mydhily-mr/aiot-inventory-predictor/docs/d8_ultrasonic.md

# Individual Sensor Testing

# Ultrasonic with MAX32630fthr

### Goal

Interfacing SSD1306 Oled display with MAX32630fthr board.

### Final working setup

**Hardware:** MAX32630FTHR, NHX711 Weight sensor 5Kg

**Wiring** :
| Weight Sensor  | MAX32630FTHR |
|---|---|
| GND | GND |
| VCC | 3V3 |
| TRIG | P5_6  |
| ECHO | P4_0  |

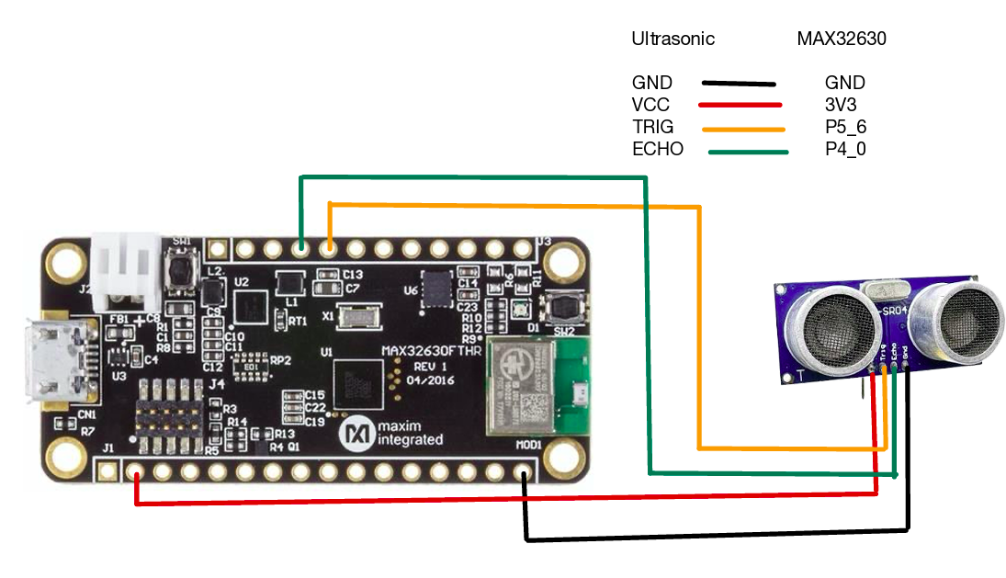
[picture p96: images/ultra_sc.png]
  — Ultrasonic Connection.

**Code Snippet:**
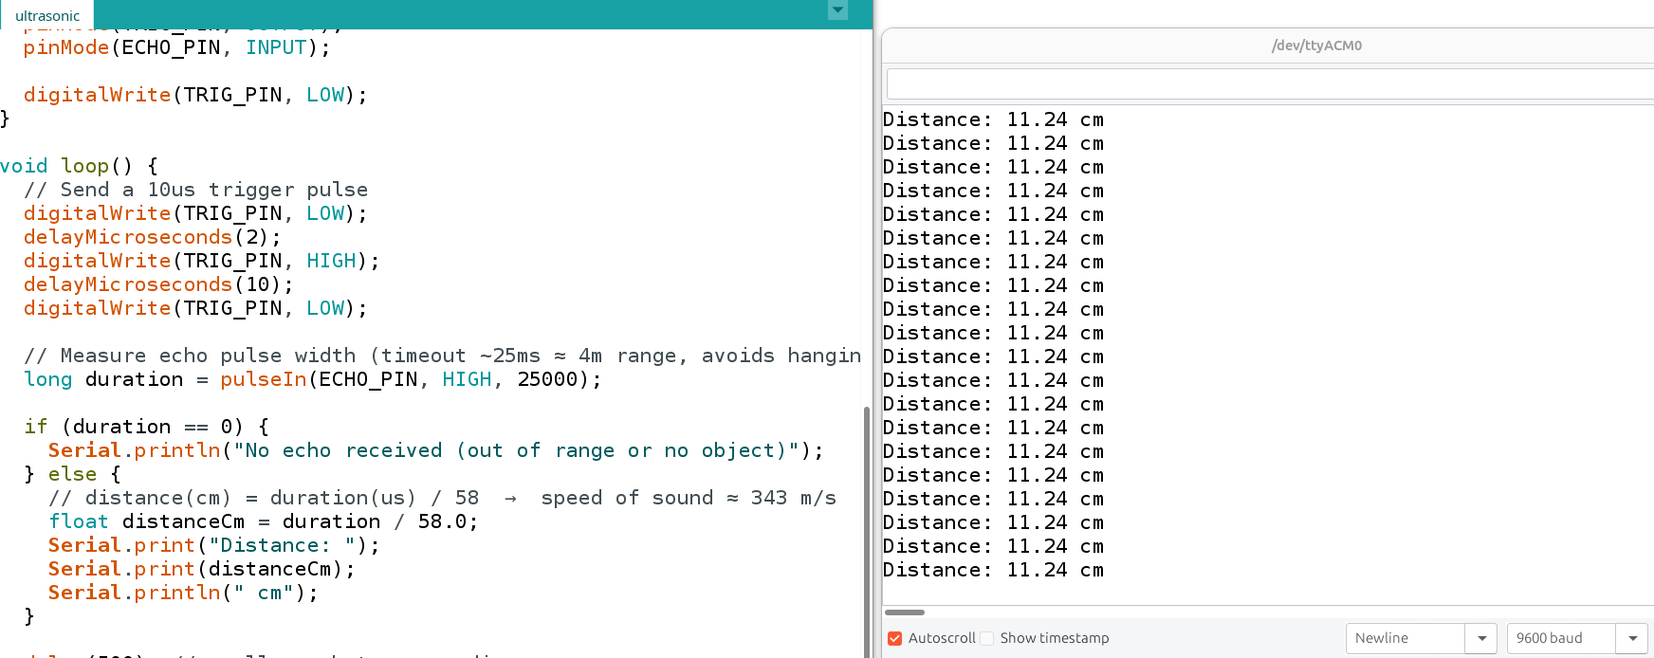
[picture p97: images/ul.png]
 — Ultrasonic
## Output:
wifi serial monitor — Ultrasonic
