mydhily-mr/aiot-inventory-predictor/docs/d10_buzzer.md

# Individual Sensor Testing

# Piezo Buzzer with MAX32630 FTHR

### Goal

Interfacing Buzzer with MAX32630fthr board.

**Schematic:**
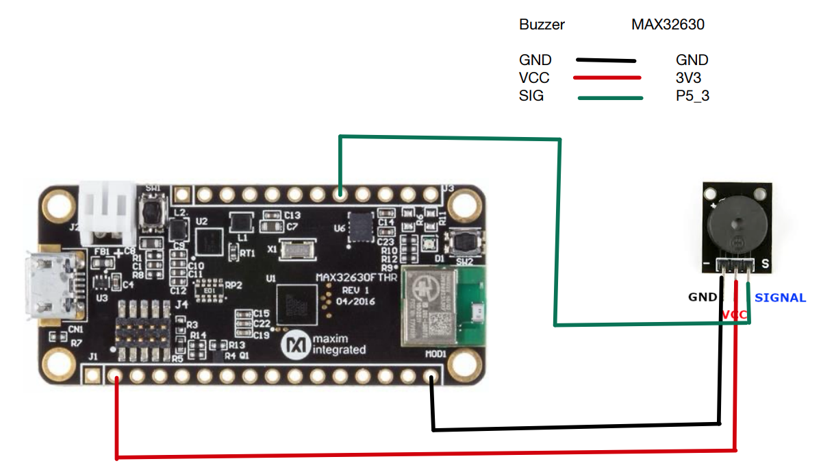
[picture p98: images/bzr.png]
 — Buzzer

**Wiring** :
| RYG  | MAX32630FTHR |
|---|---|
| GND | GND |
| VCC | 3V3 |
| SIG | P5_3  |

**Code Snippet:**
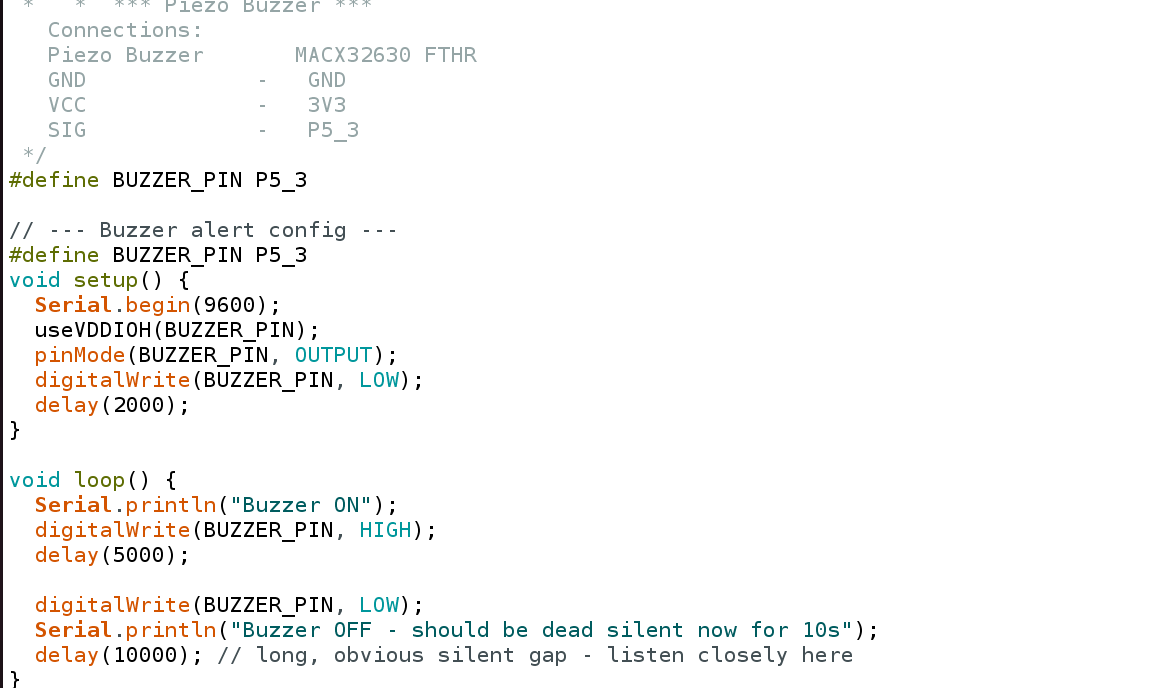
[picture p99: images/bzr_cd.png]
 —Buzzer
