mydhily-mr/aiot-inventory-predictor/docs/d12_pir.md

# Individual Sensor Testing

# PIR with MAX32630 FTHR

### Goal

Interfacing PIR  with MAX32630fthr board.

**Schematic:**
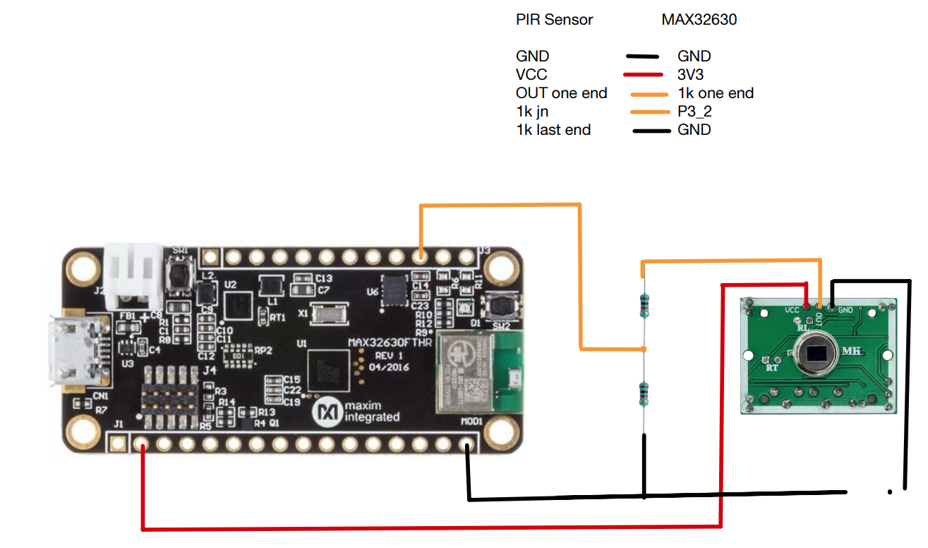
[picture p100: images/pir.png]
ryg led
 — PIR
