mydhily-mr/aiot-inventory-predictor/docs/d6_weight_sensor.md

# Individual Sensor Testing

# HX711 Weight Sensor with MAX32630FTHR board

### Goal

Interfacing HX711 weight sensor with MAX32630fthr board.

### Final working setup

**Hardware:** MAX32630FTHR, NHX711 Weight sensor 5Kg

**Wiring** :
| Weight Sensor  | MAX32630FTHR |
|---|---|
| GND | GND |
| VCC | 3V3 |
| DT | P5_5 (pin 45 in software) |
| DSCK  | P5_4 (pin 45 in software) |

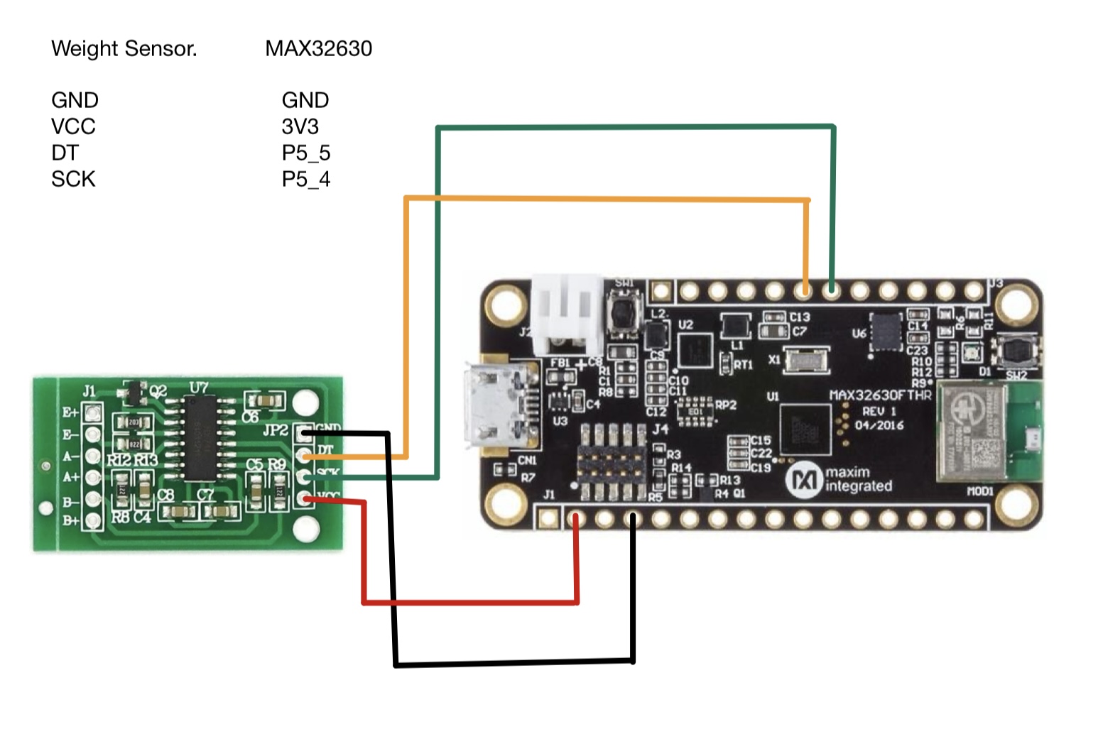
[picture p101: images/weight_sensor.PNG]
  — weight_sensor Connection.

**Code Snippet:**
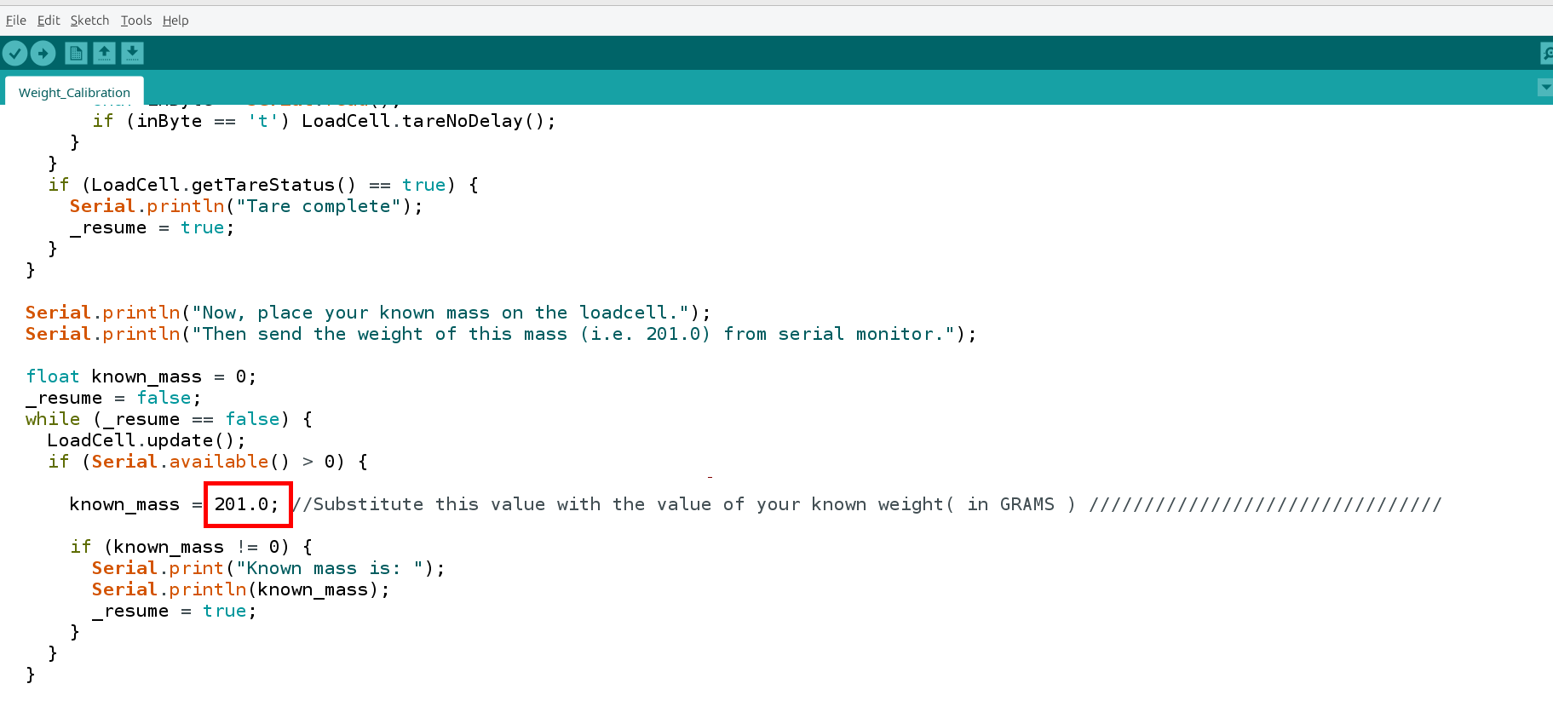
[picture p102: images/weight_sens.png]
 — weight_sensor Known mass value to change.

## Output:

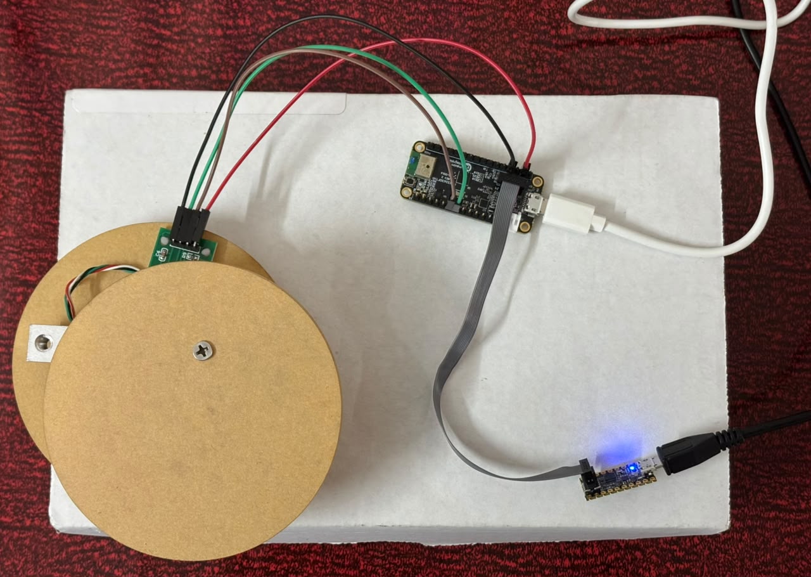
[picture p103: images/weight_output1.jpeg]
  — weight_sensor connection.

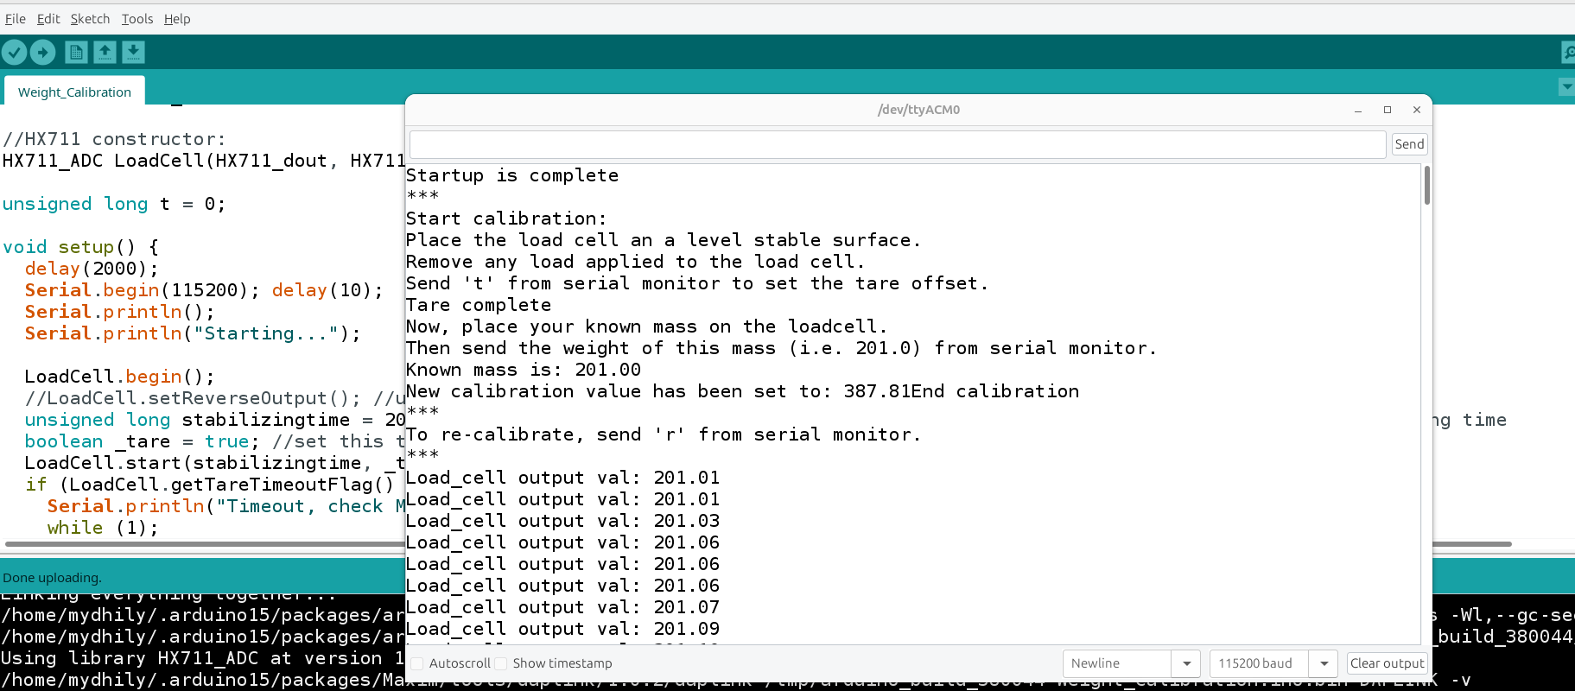
[picture p104: images/weight_sensor_output.png]
  — weight_sensor calibration output with known weight.

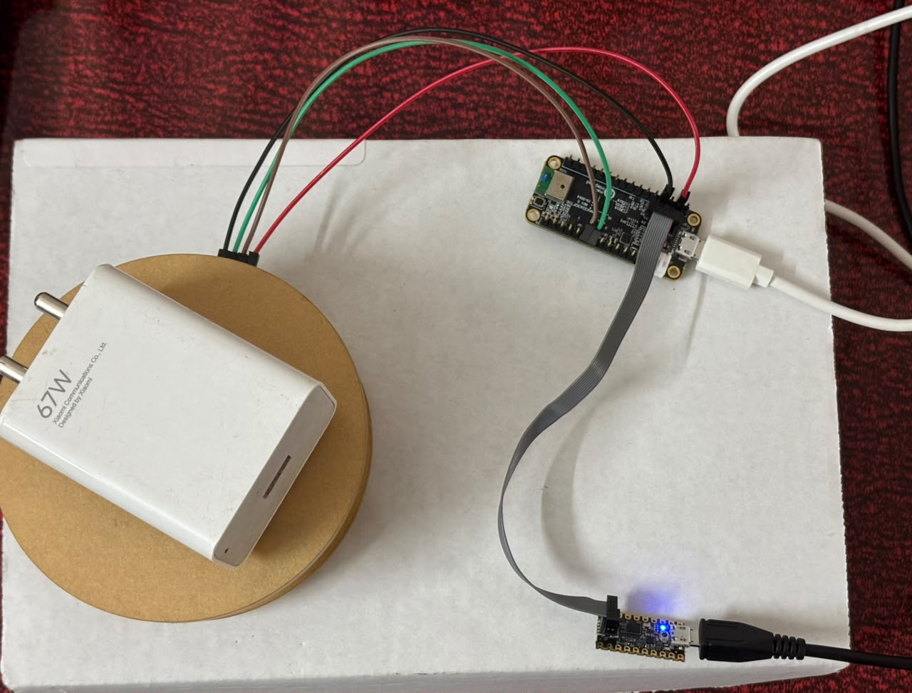
[picture p105: images/weight_output2.jpeg]
wifi firebase
 — weight_sensor  output for objects with unknown weights.

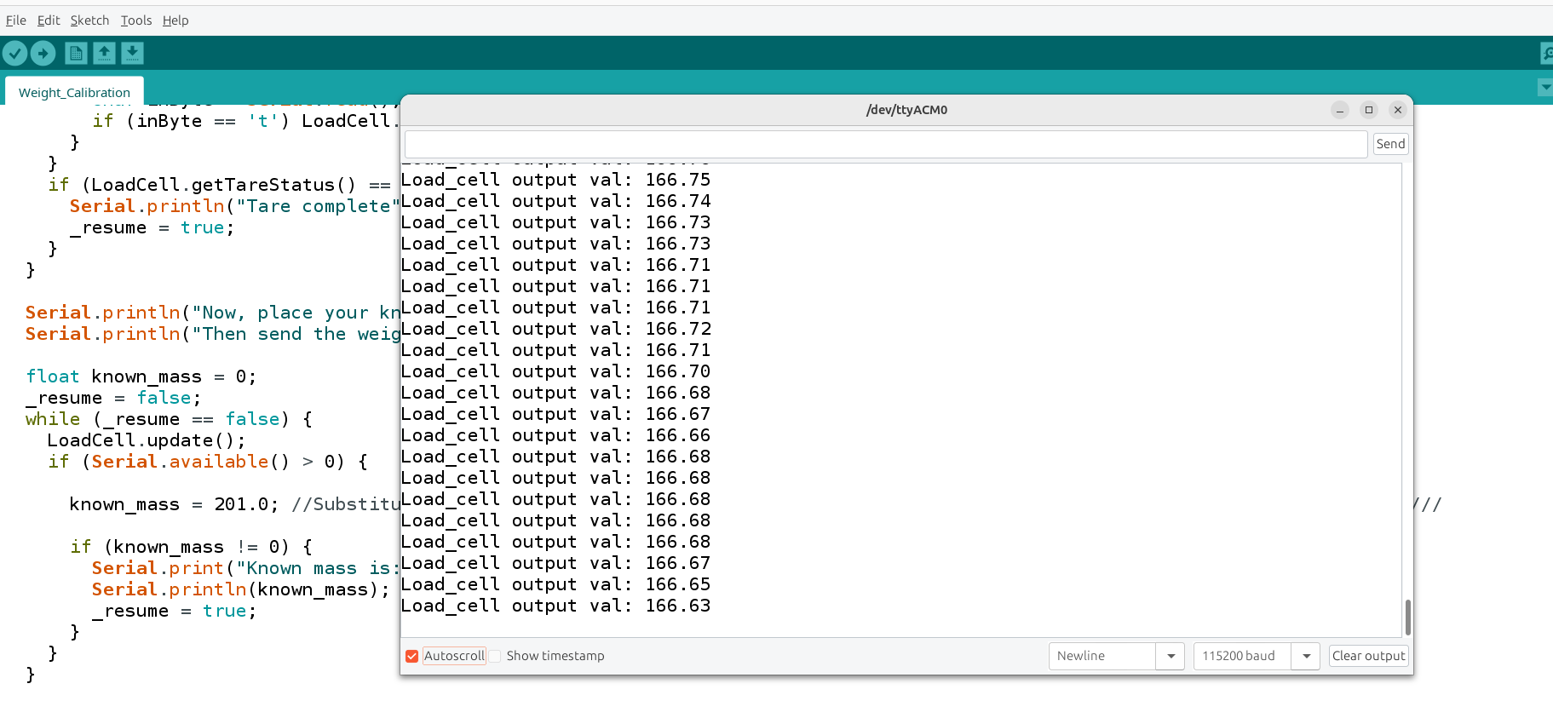
[picture p106: images/weight_output3.png]
  — weight_sensor  output for objects with unknown weights.
