mydhily-mr/aiot-inventory-predictor/docs/d7_oled.md

# Individual Sensor Testing

# OLED Display with MAX32630FTHR Board

### Goal

Interfacing SSD1306 Oled display with MAX32630fthr board.

### Final working setup

**Hardware:** MAX32630FTHR, NHX711 Weight sensor 5Kg

**Wiring** :
| Weight Sensor  | MAX32630FTHR |
|---|---|
| GND | GND |
| VCC | 3V3 |
| SDA | P3_4 (pin 28 in software) |
| SCL | P3_5 (pin 29 in software) |

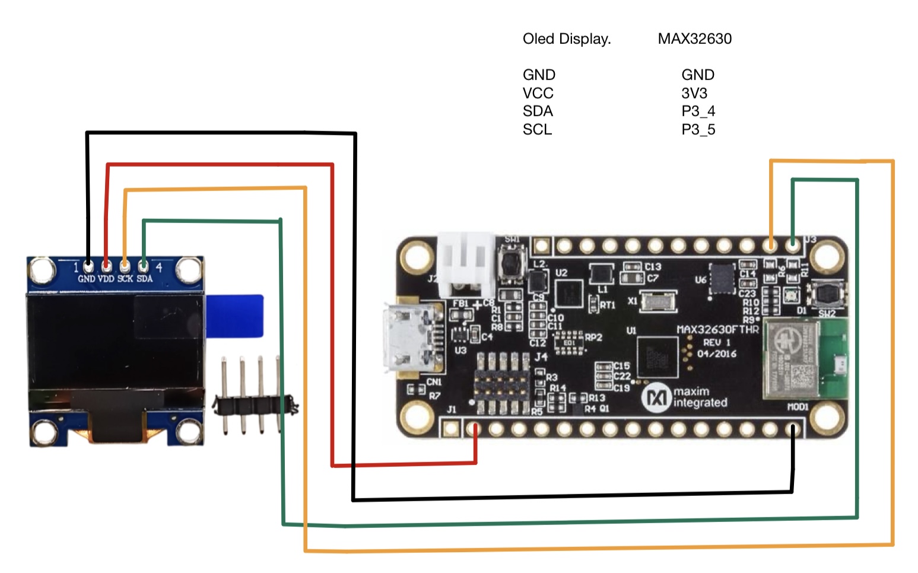
[picture p107: images/d7_oled.PNG]
  — OLED display Connection.

**Code Snippet:**
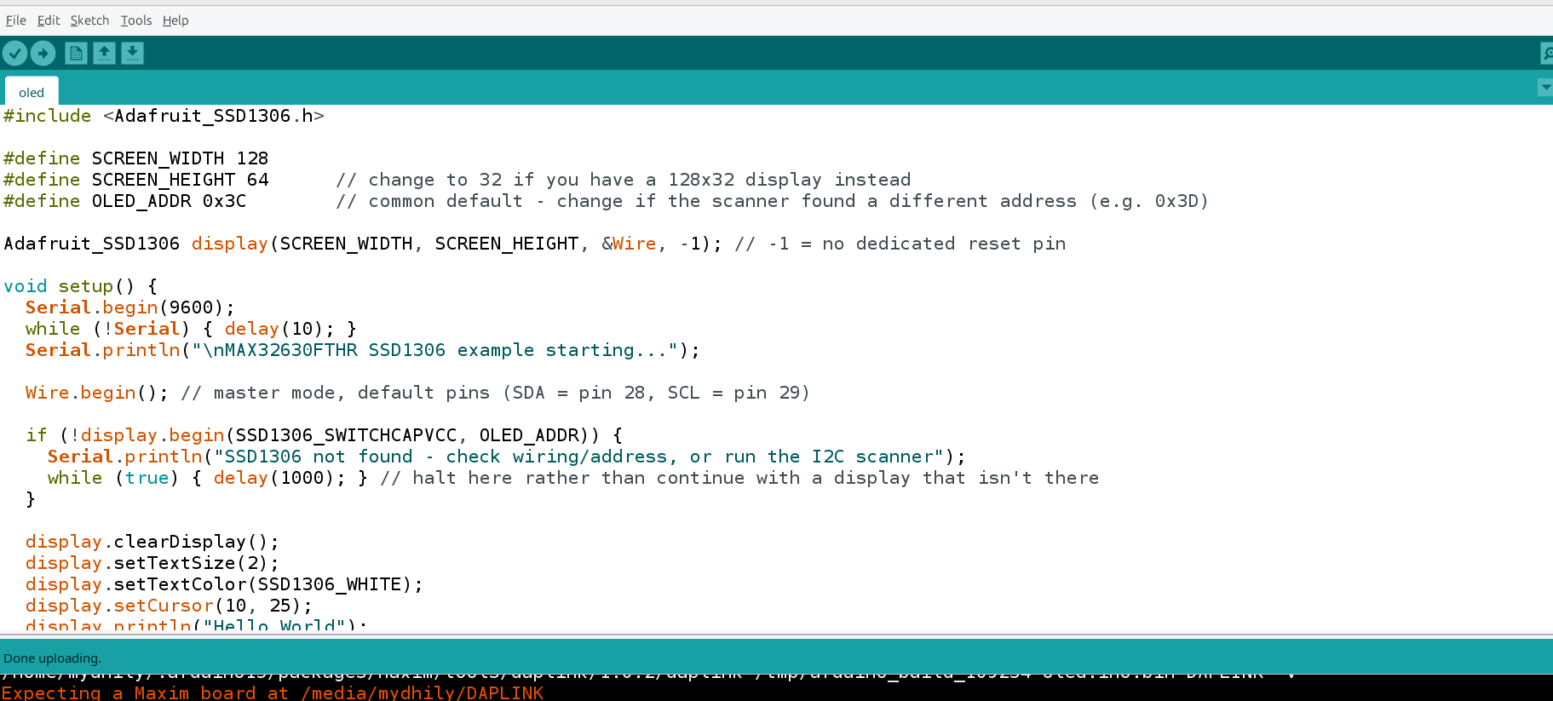
[picture p108: images/d7_oled2.png]
 — Oled display
## Output:

  wifi serial monitor— OLED output
