mydhily-mr/aiot-inventory-predictor/docs/d11_ir.md

# Individual Sensor Testing

# IR Sensor with MAX32630 FTHR

### Goal

Interfacing IR Sensor  with MAX32630fthr board.

### Final working setup

**Schematic:**
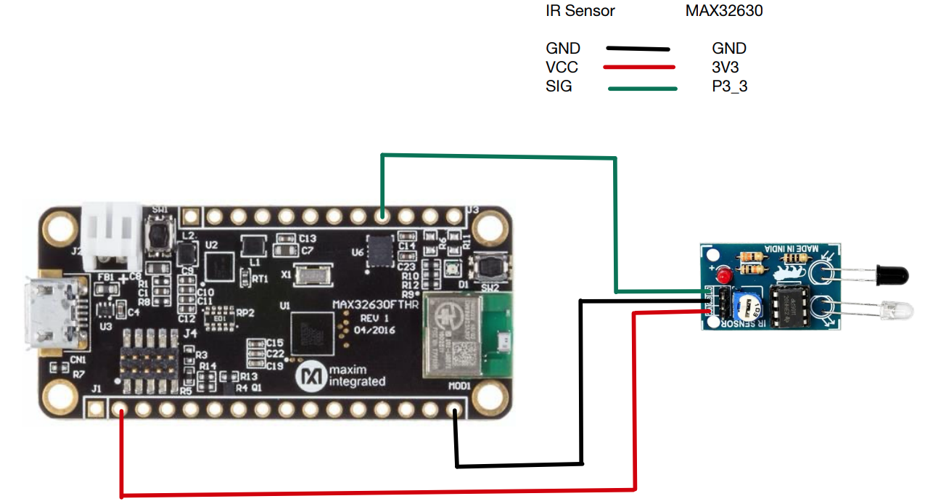
[picture p112: images/ir.png]
ryg led
 — RYG

**Wiring** :
| IR  | MAX32630FTHR |
|---|---|
| GND | GND |
| VCC | P5_0 |
| O/P | P3_3  |
