mydhily-mr/aiot-inventory-predictor/docs/na_bakup_camera.md

# Individual Sensor Testing

# Camera

### Goal

Interfacing Camera Module  with MAX32630fthr board.

### Final working setup

**Hardware:** MAX32630FTHR, Raspberry Pi Camera Module, Grove Vision AI Module v2

**Training:**
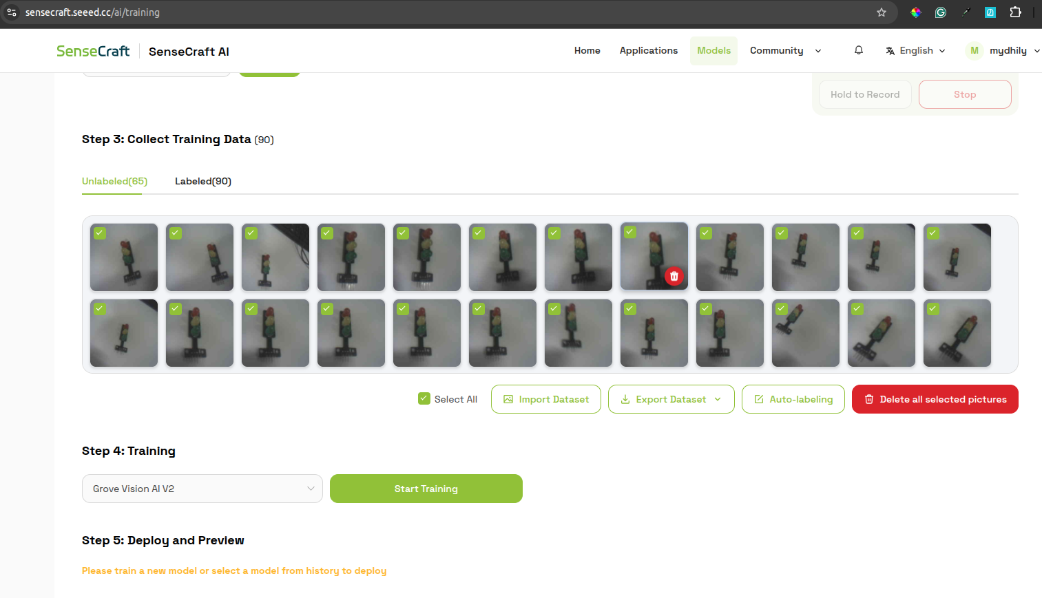
[picture p119: images/cam1.png]
 — Camera Module

 **Training:**
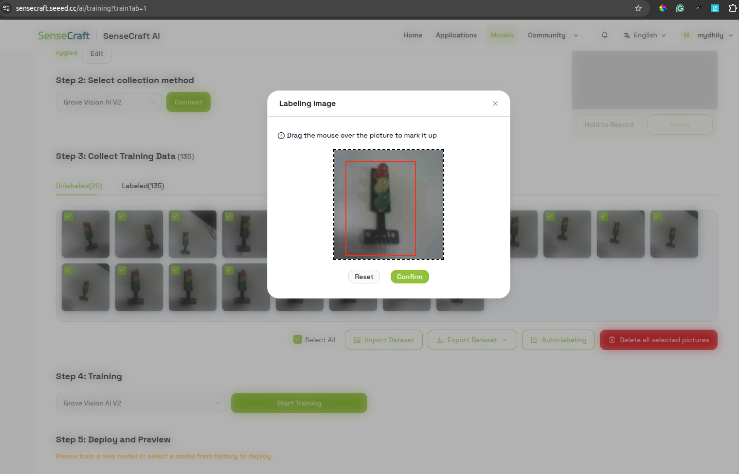
[picture p120: images/cam2.png]
 — Camera Module

 **Training:**
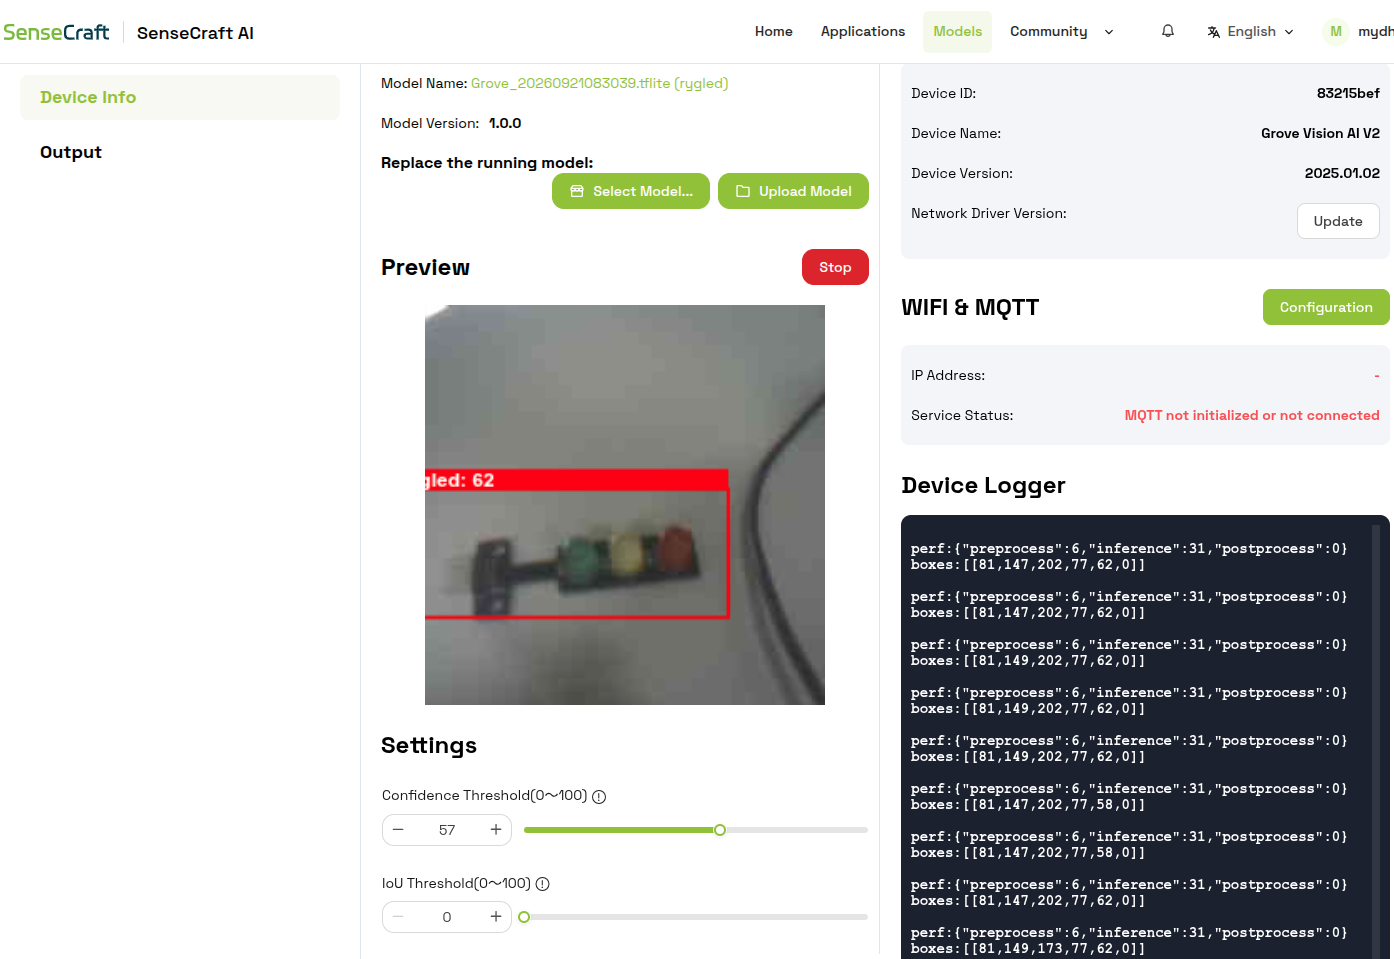
[picture p121: images/cam3.png]
 — Camera Module
