mydhily-mr/aiot-inventory-predictor/case_design_files/aiot_case_v6_fusion360/sensors_placed_preview_v6.png

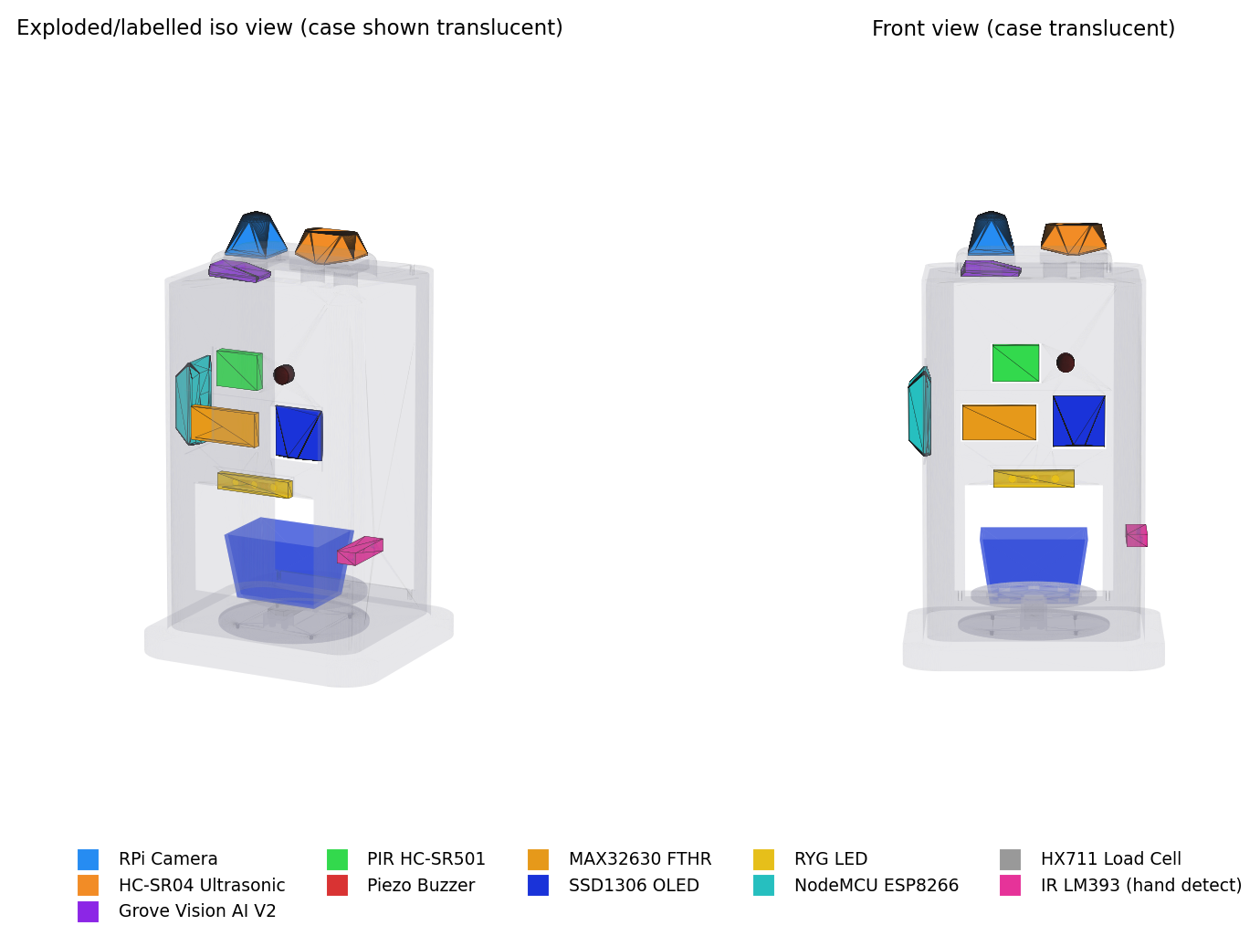
case_design_files/aiot_case_v6_fusion360/sensors_placed_preview_v6.png
