mydhily-mr/aiot-inventory-predictor/images/a1.png

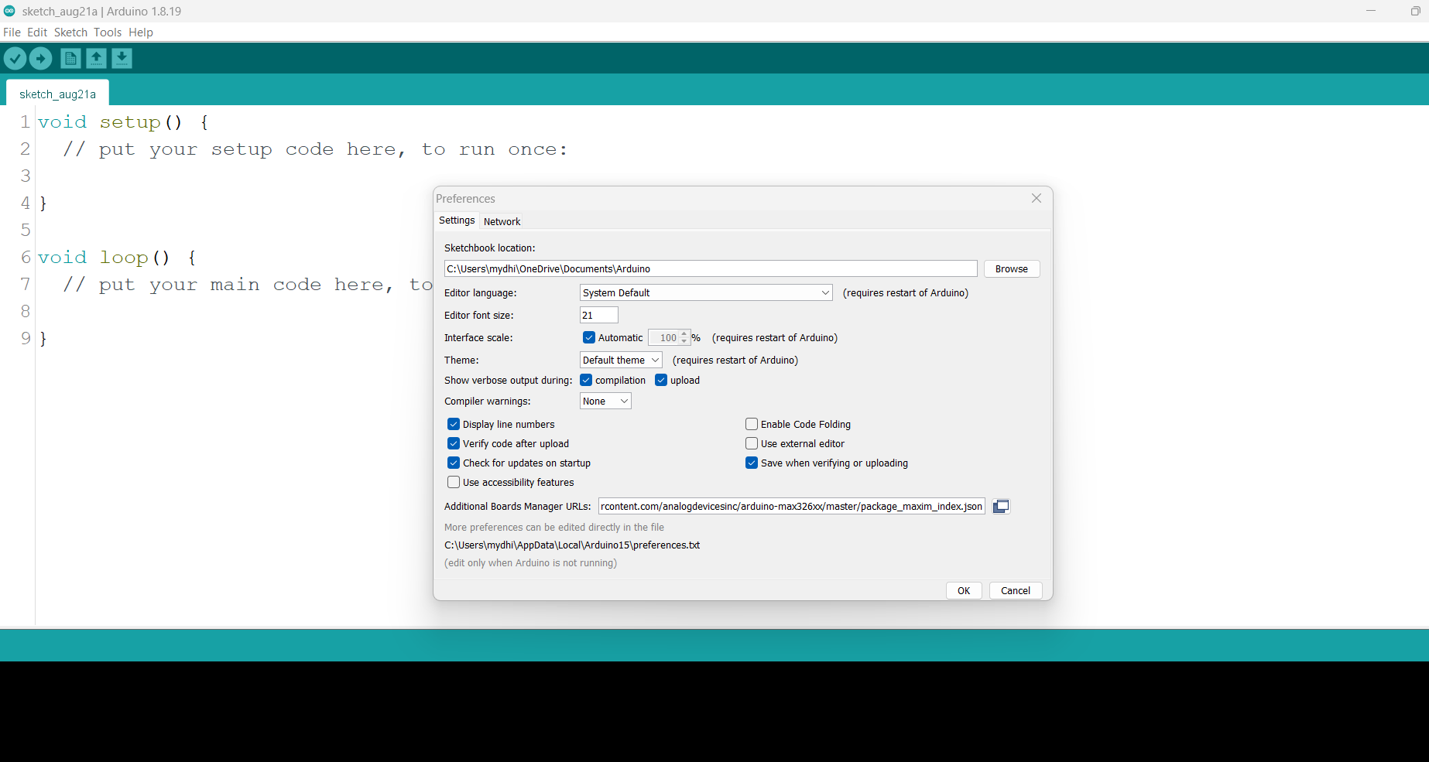
images/a1.png
