mydhily-mr/aiot-inventory-predictor/images/a2.png

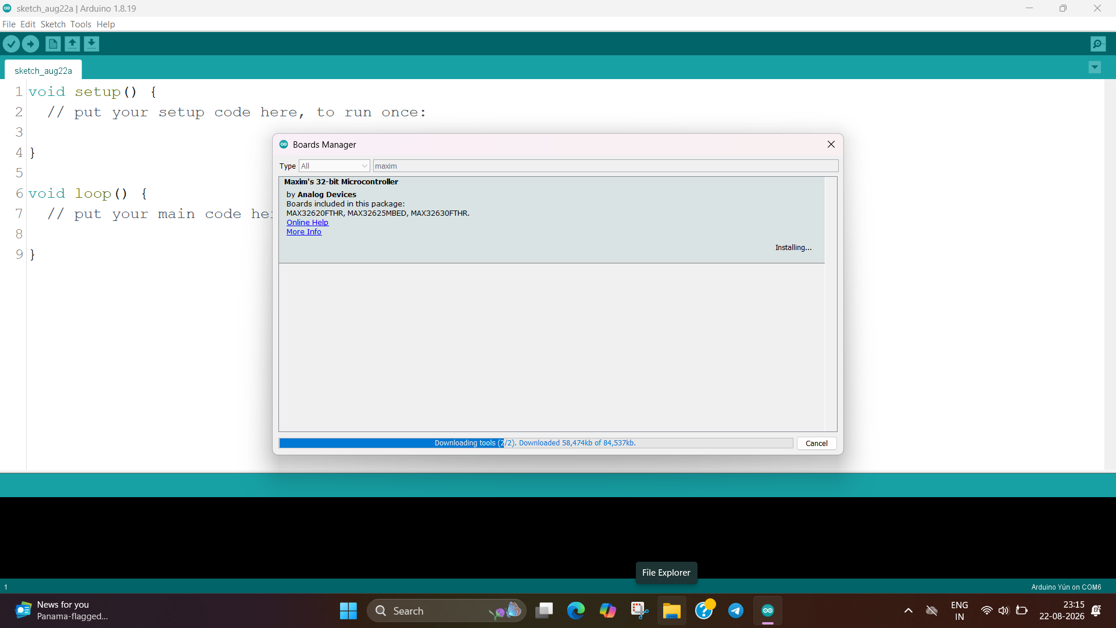
images/a2.png
