mydhily-mr/aiot-inventory-predictor/images/d8_cam1.jpeg

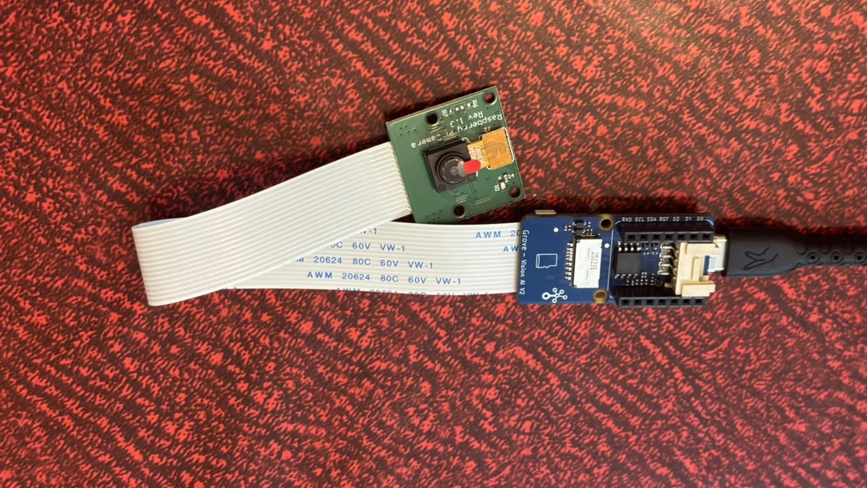
images/d8_cam1.jpeg
