mydhily-mr/aiot-inventory-predictor/images/demo.gif

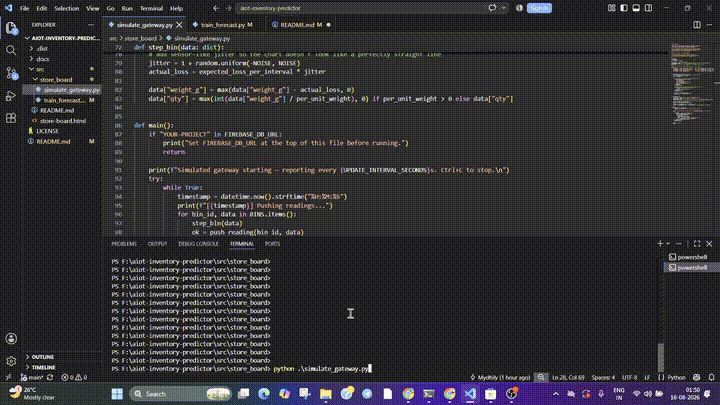
images/demo.gif
