mydhily-mr/aiot-inventory-predictor/images/flow_chart.png

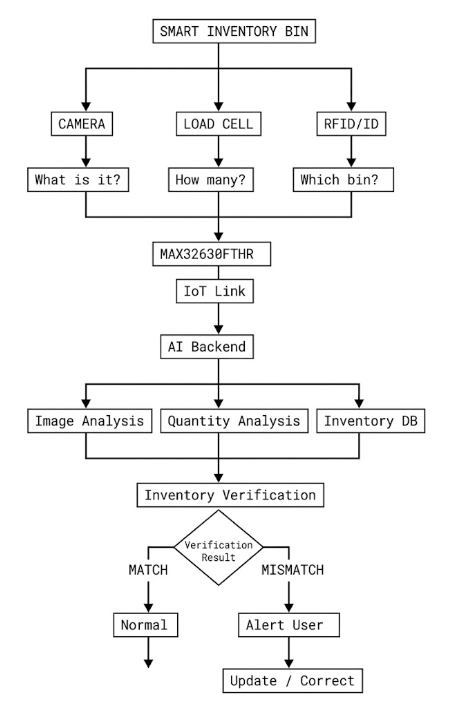
images/flow_chart.png
