mydhily-mr/aiot-inventory-predictor/images/image8.jpg

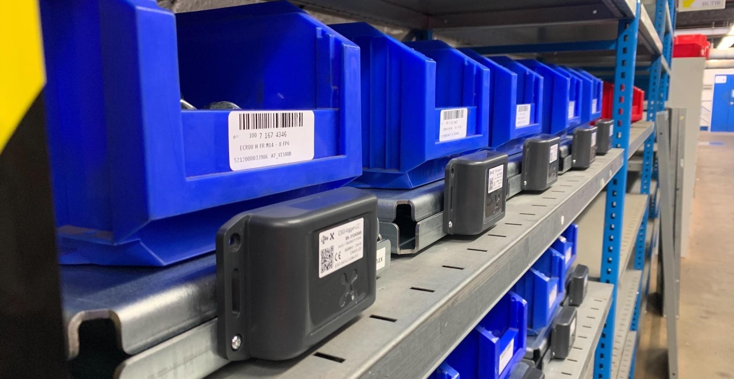
images/image8.jpg
