mydhily-mr/aiot-inventory-predictor/images/image9.jpg

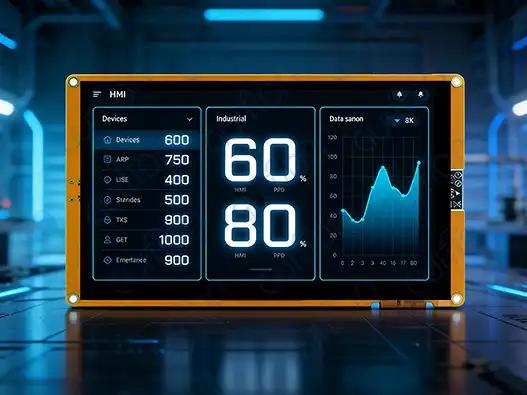
images/image9.jpg
