mydhily-mr/aiot-inventory-predictor/images/output.png

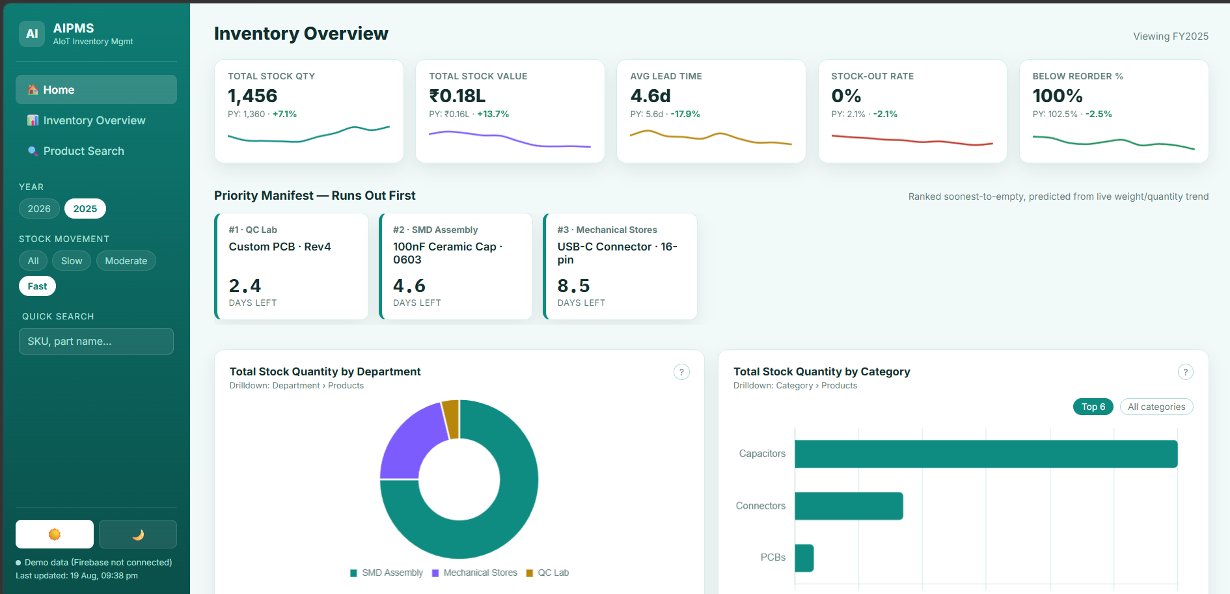
images/output.png
