mydhily-mr/aiot-inventory-predictor/images/setbrd2.png

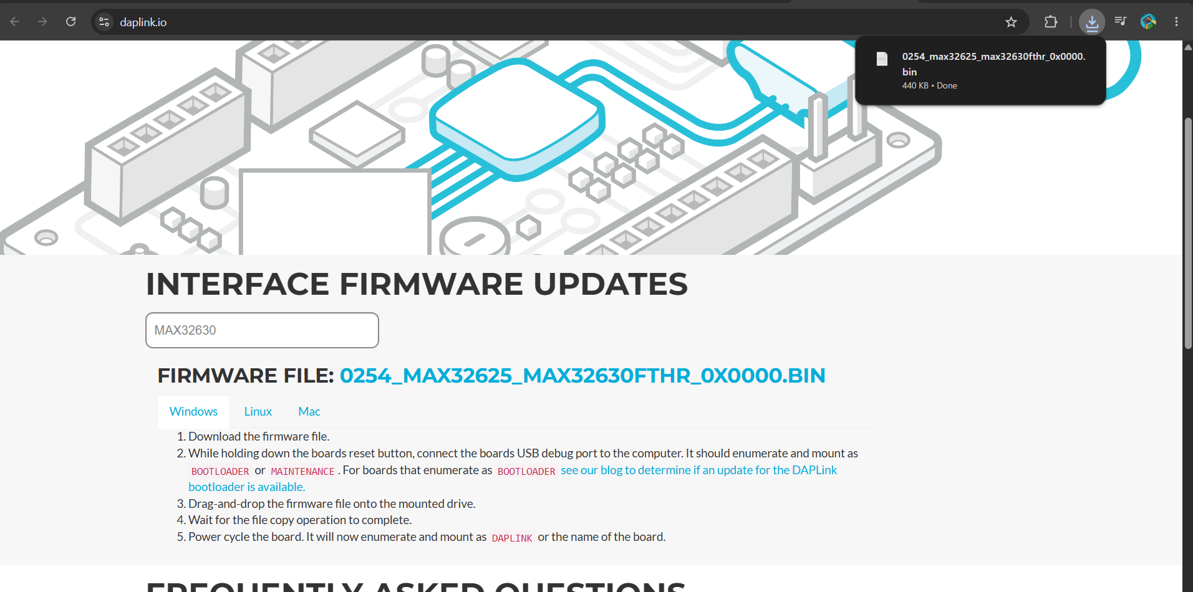
images/setbrd2.png
