mydhily-mr/aiot-inventory-predictor/images/setbrd3.png

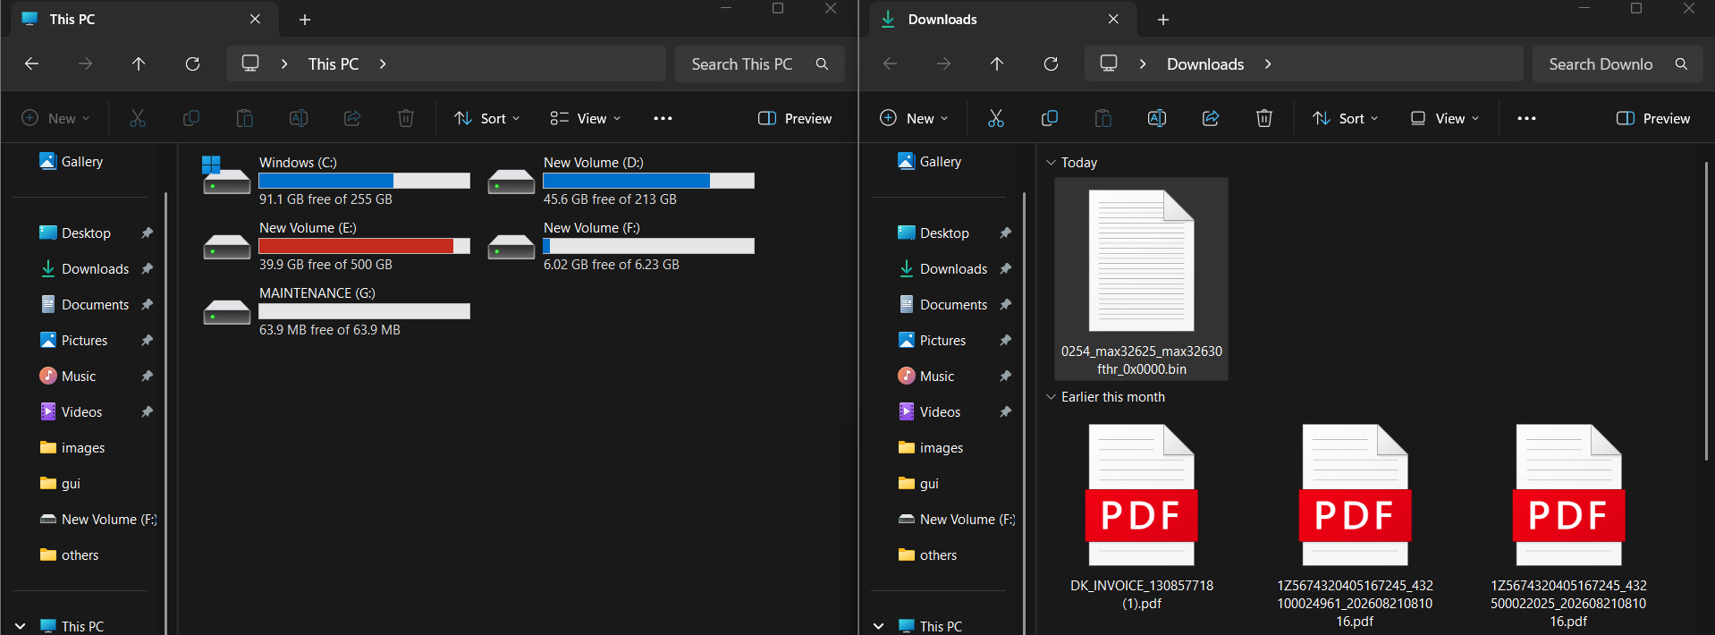
images/setbrd3.png
