mydhily-mr/aiot-inventory-predictor/images/template_pics/10a.png

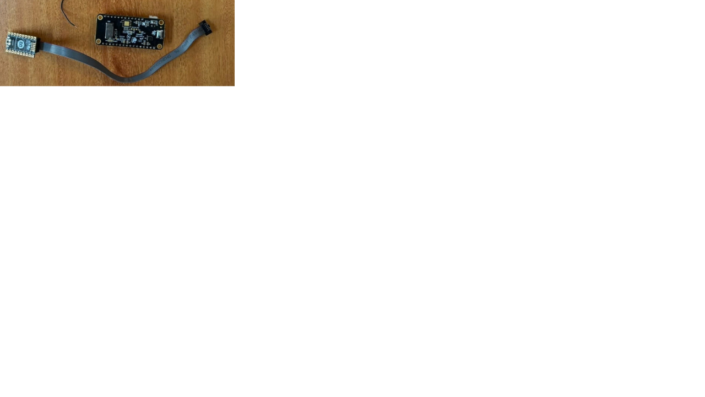
images/template_pics/10a.png
