mydhily-mr/aiot-inventory-predictor/images/template_pics/11a.gif

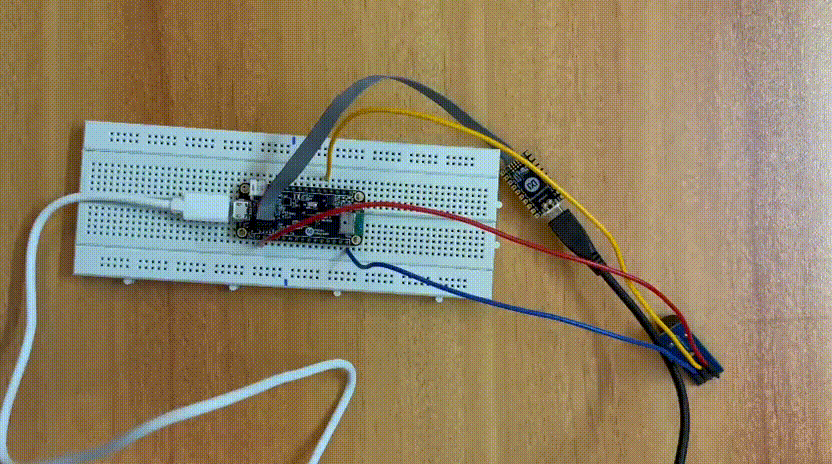
images/template_pics/11a.gif
