mydhily-mr/aiot-inventory-predictor/images/template_pics/39.png

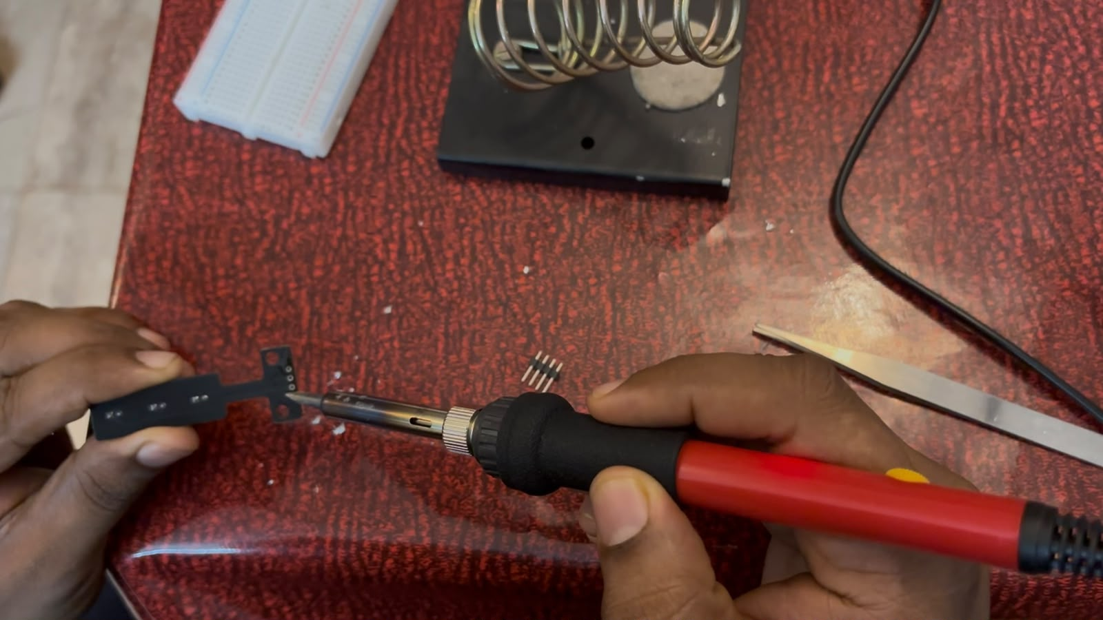
images/template_pics/39.png
