mydhily-mr/aiot-inventory-predictor/images/template_pics/40.png

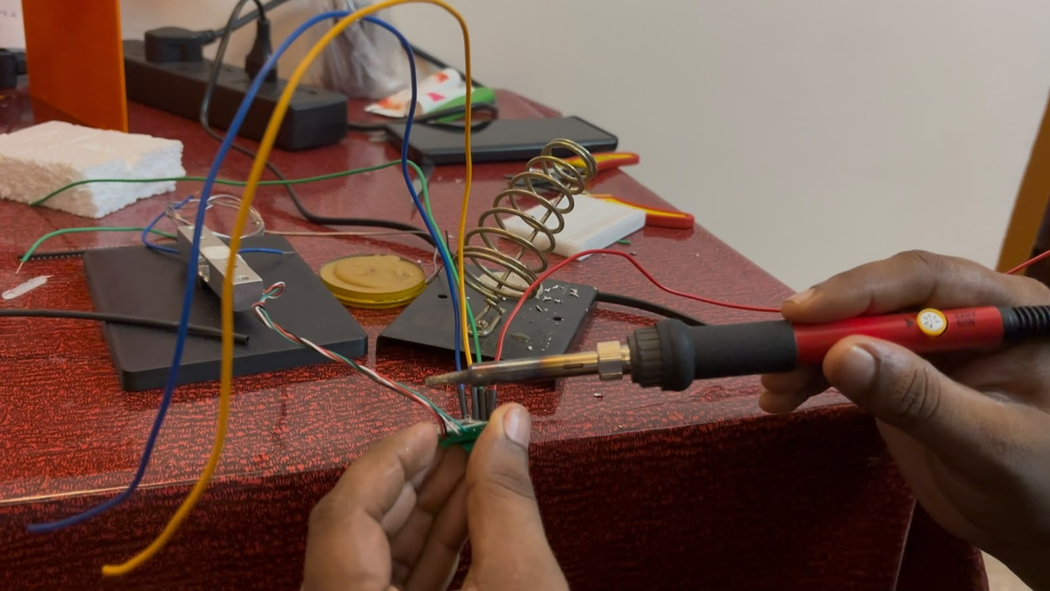
images/template_pics/40.png
