mydhily-mr/aiot-inventory-predictor/images/template_pics/48a.gif

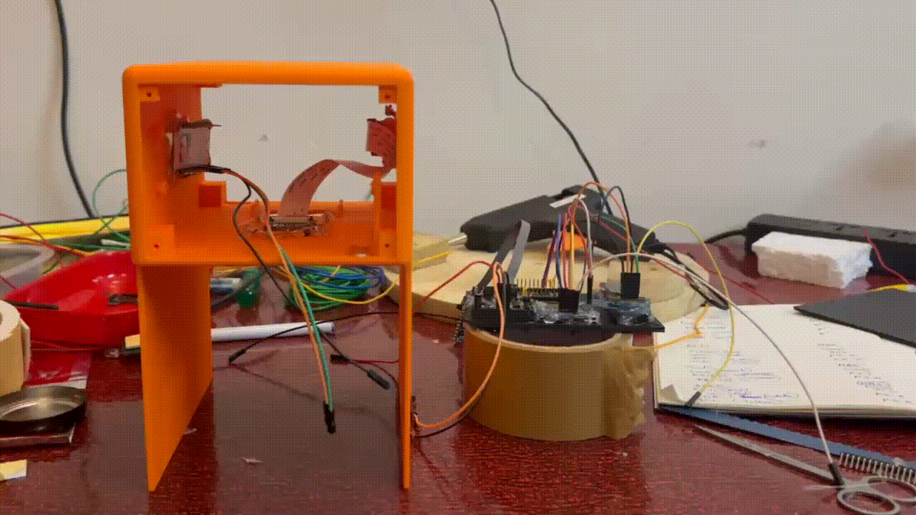
images/template_pics/48a.gif
