mydhily-mr/aiot-inventory-predictor/images/template_pics/a13.jpeg

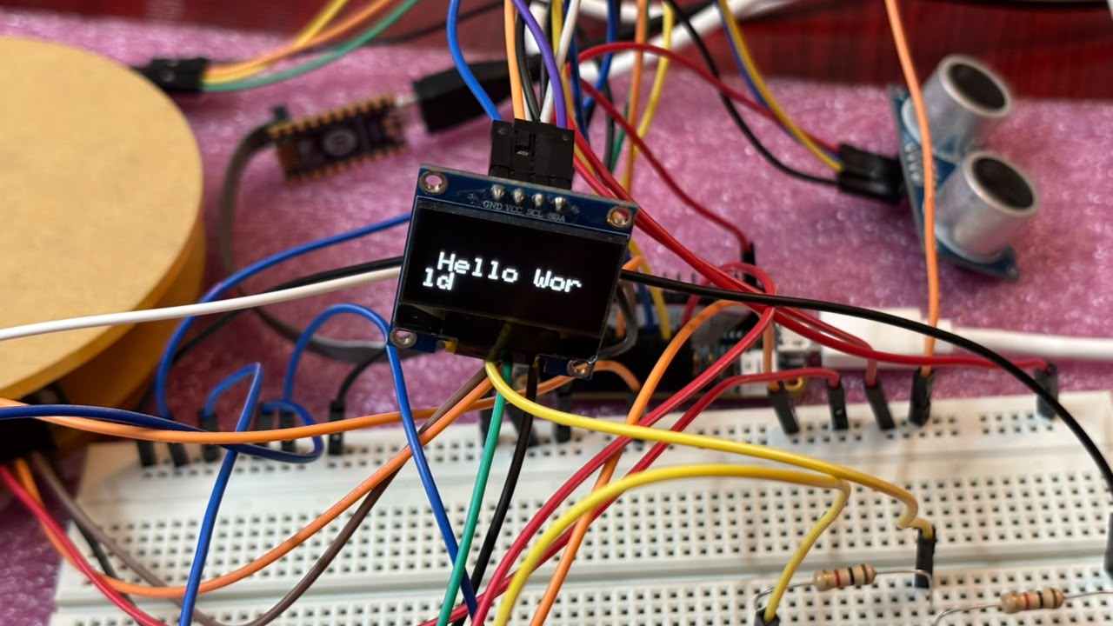
images/template_pics/a13.jpeg
