mydhily-mr/aiot-inventory-predictor/images/template_pics/a40.png

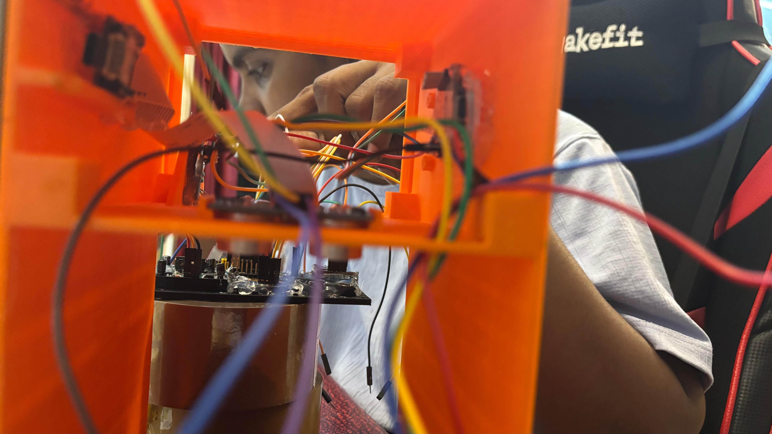
images/template_pics/a40.png
