mydhily-mr/aiot-inventory-predictor/images/template_pics/a53.png

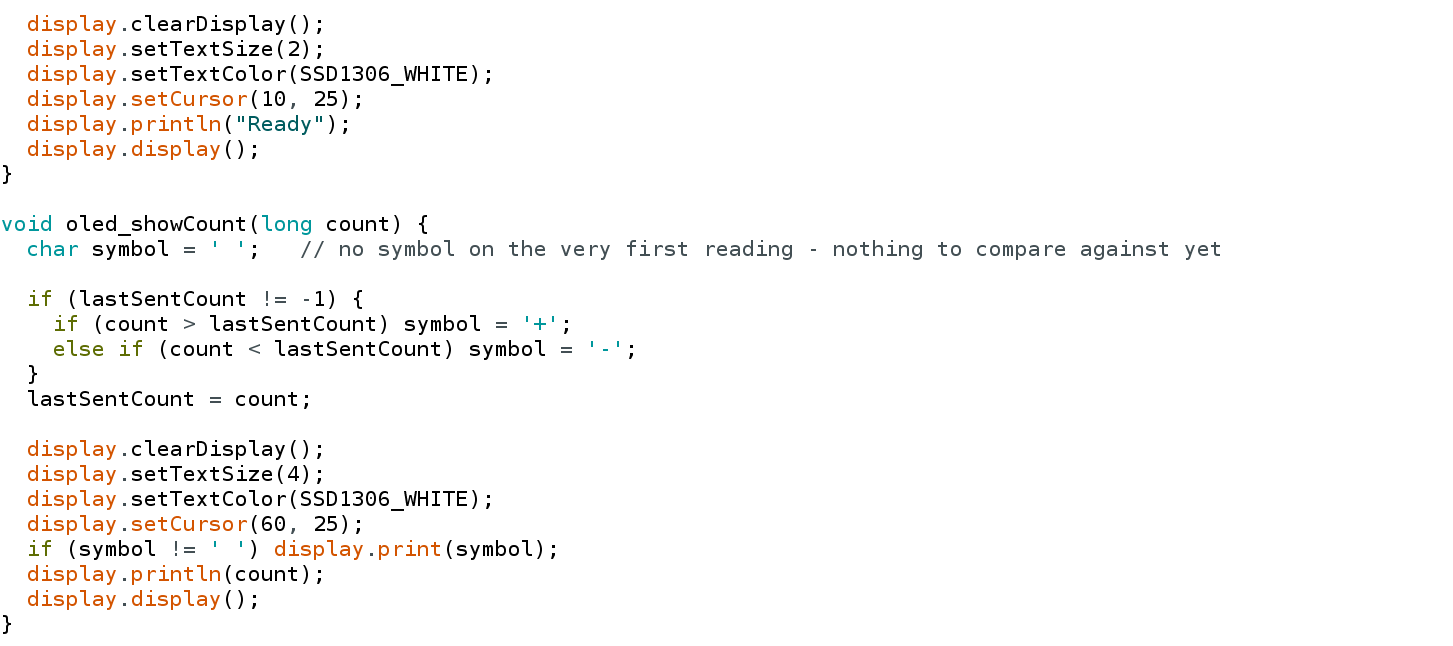
images/template_pics/a53.png
