mydhily-mr/aiot-inventory-predictor/images/ultra.png

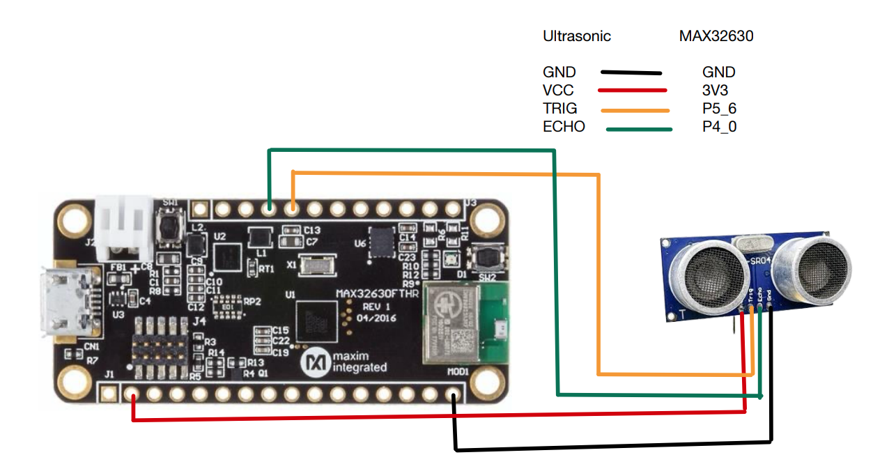
images/ultra.png
