mydhily-mr/aiot-inventory-predictor/case_design_files/AIoT_case_v5/AIoT_case_v5/STEP_for_Fusion360/07b_camera_plate_wide_ALT.step

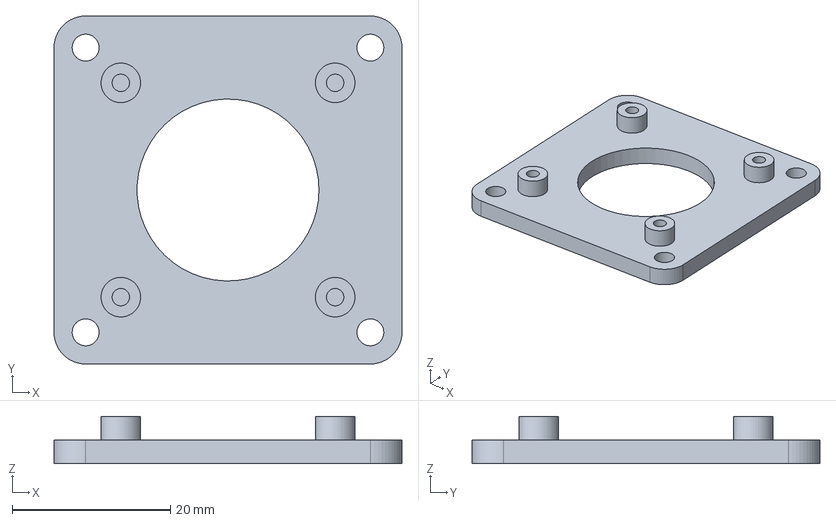
[picture p234: CAD file, 2026-09-22]
case_design_files/AIoT_case_v5/AIoT_case_v5/STEP_for_Fusion360/07b_camera_plate_wide_ALT.step
44.0 x 44.0 x 6.00 mm
