mydhily-mr/aiot-inventory-predictor/case_design_files/AIoT_case_v5/AIoT_case_v5/print_ready_STL/08_storage_bin.stl

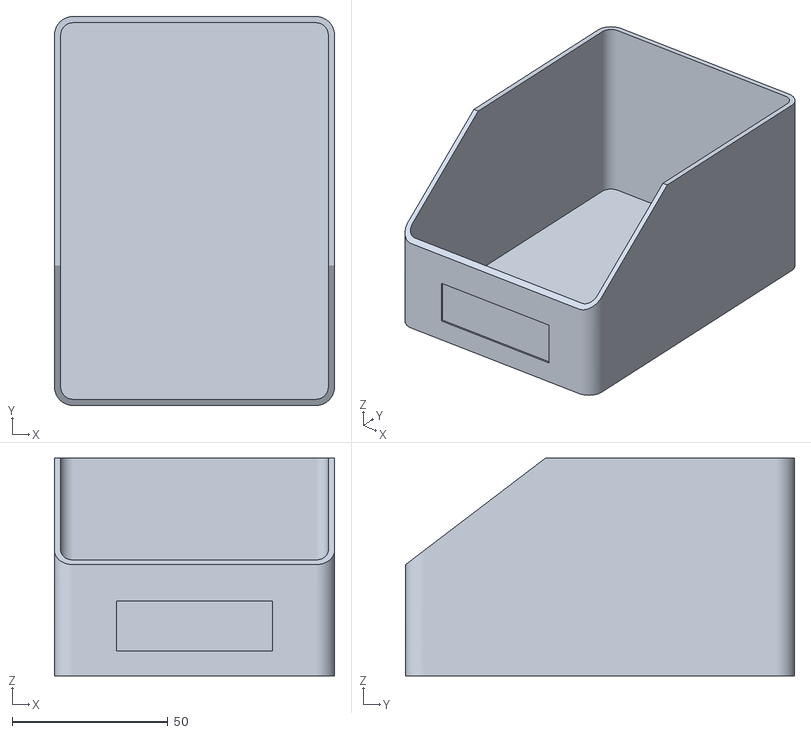
[picture p235: CAD file, 2026-09-22]
case_design_files/AIoT_case_v5/AIoT_case_v5/print_ready_STL/08_storage_bin.stl
90.0 x 125.0 x 70.0
