mydhily-mr/aiot-inventory-predictor/case_design_files/AIoT_case_v5/AIoT_case_v5/print_ready_STL/07_camera_plate_std_OV5647.stl

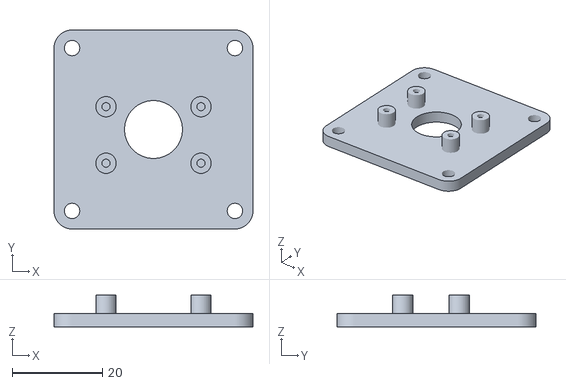
[picture p236: CAD file, 2026-09-22]
case_design_files/AIoT_case_v5/AIoT_case_v5/print_ready_STL/07_camera_plate_std_OV5647.stl
44.0 x 44.0 x 7.00
