mydhily-mr/aiot-inventory-predictor/case_design_files/AIoT_case_v5/AIoT_case_v5/STEP_for_Fusion360/01_tower_body.step

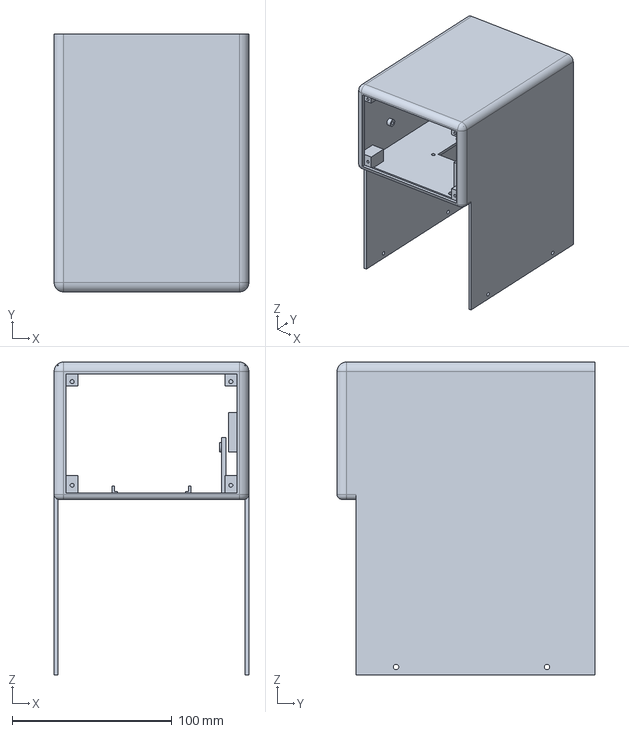
[picture p237: CAD file, 2026-09-22]
case_design_files/AIoT_case_v5/AIoT_case_v5/STEP_for_Fusion360/01_tower_body.step
122.0 x 161.5 x 196.0 mm
