mydhily-mr/aiot-inventory-predictor/case_design_files/AIoT_case_v5/AIoT_case_v5/renders/7_print_orientation.png

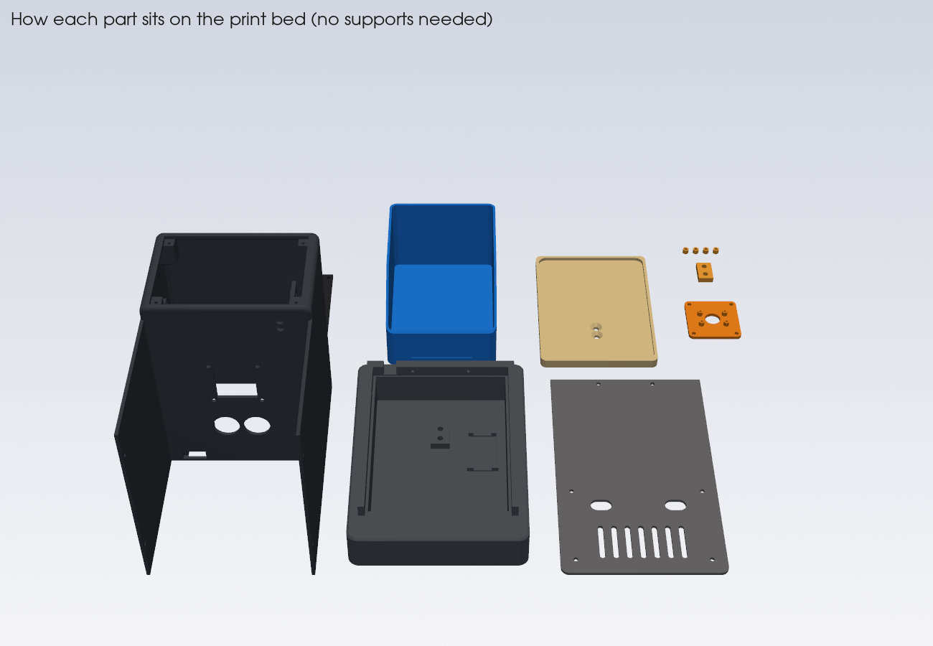
case_design_files/AIoT_case_v5/AIoT_case_v5/renders/7_print_orientation.png
