mydhily-mr/aiot-inventory-predictor/images/ryg_sc.png

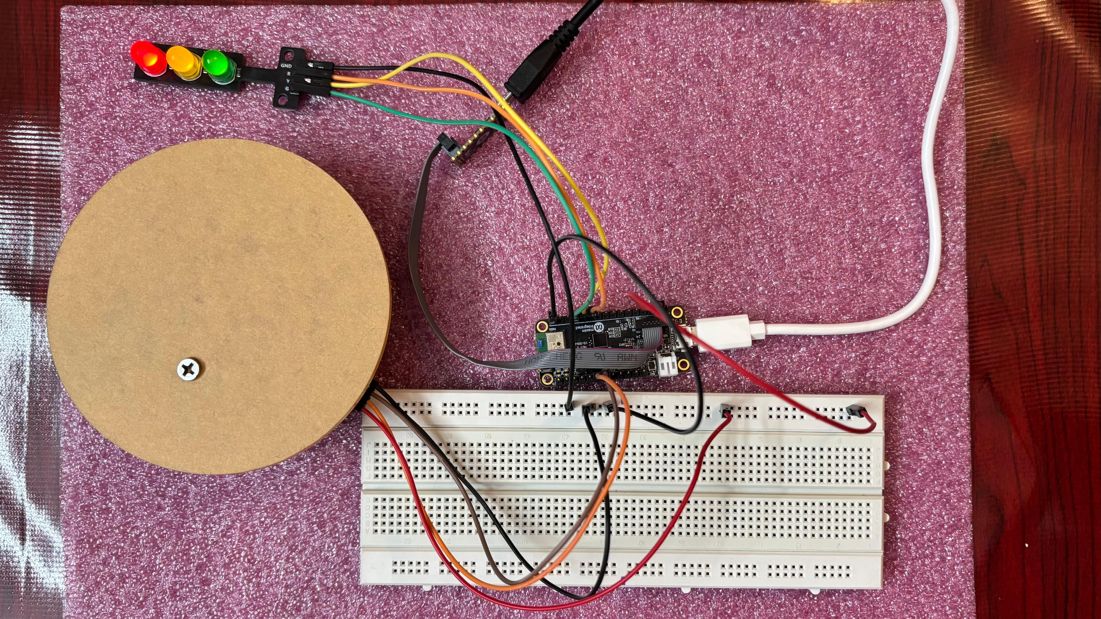
[picture p111: images/ryg_sc.png]
images/ryg_sc.png
